M8daGr8/Whiteboard-Eraser/Eraser/STL/PenHolderTop.stl

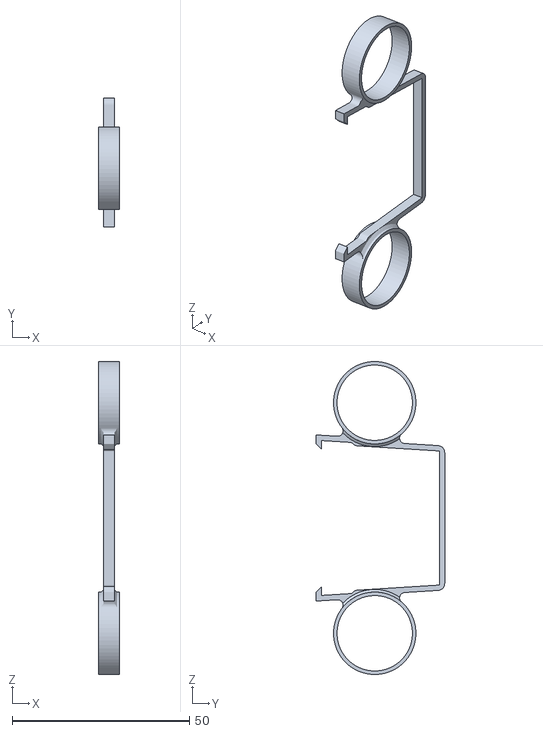
[picture p26: CAD file, 2020-11-18]
Eraser/STL/PenHolderTop.stl
6.00 x 36.2 x 88.2
