M8daGr8/Whiteboard-Eraser/Eraser/STL/Y-Axis_Wheel(8x4mm).stl

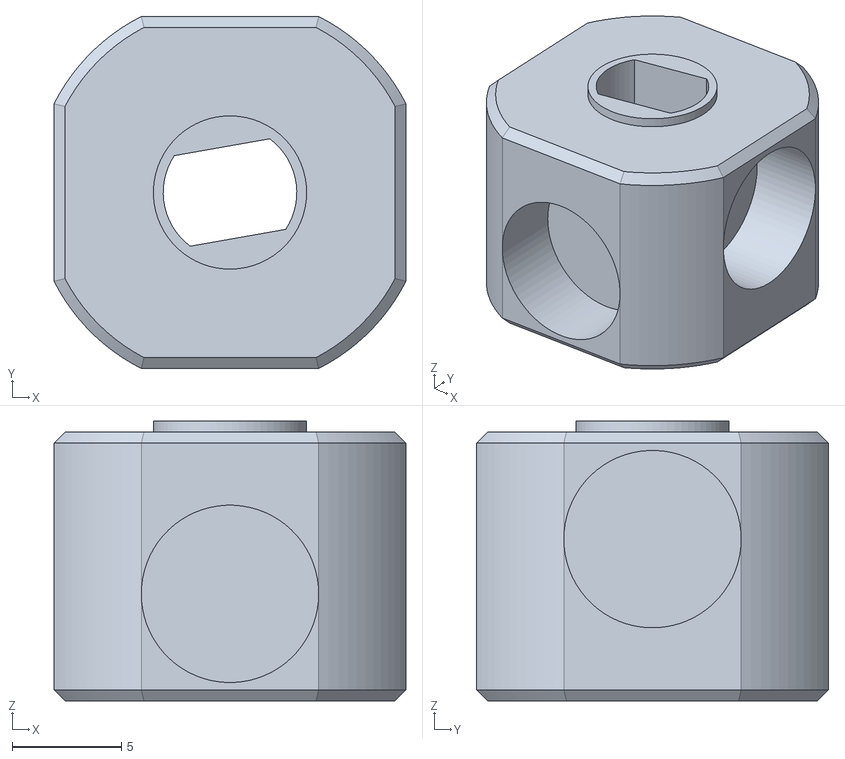
[picture p27: CAD file, 2020-11-18]
Eraser/STL/Y-Axis_Wheel(8x4mm).stl
16.1 x 16.1 x 12.8
