M8daGr8/Whiteboard-Eraser/Eraser/STL/Y-Axis_Wheel(10x10x5mm).stl

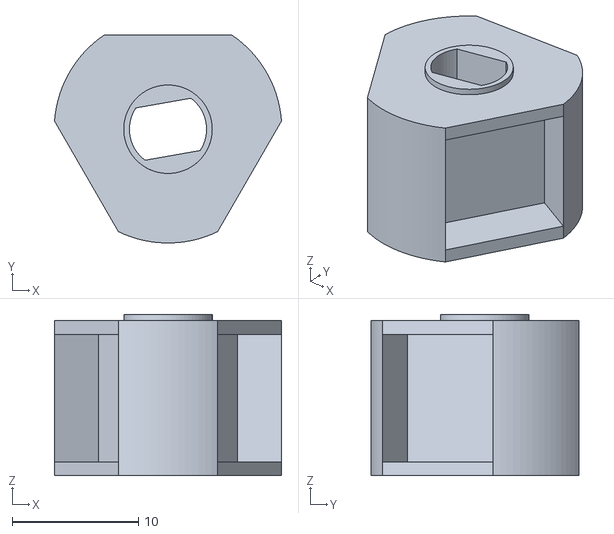
[picture p28: CAD file, 2020-11-18]
Eraser/STL/Y-Axis_Wheel(10x10x5mm).stl
18.0 x 16.4 x 12.8
